papsdroidfr/piClock/_docs/20200311_220712.jpg

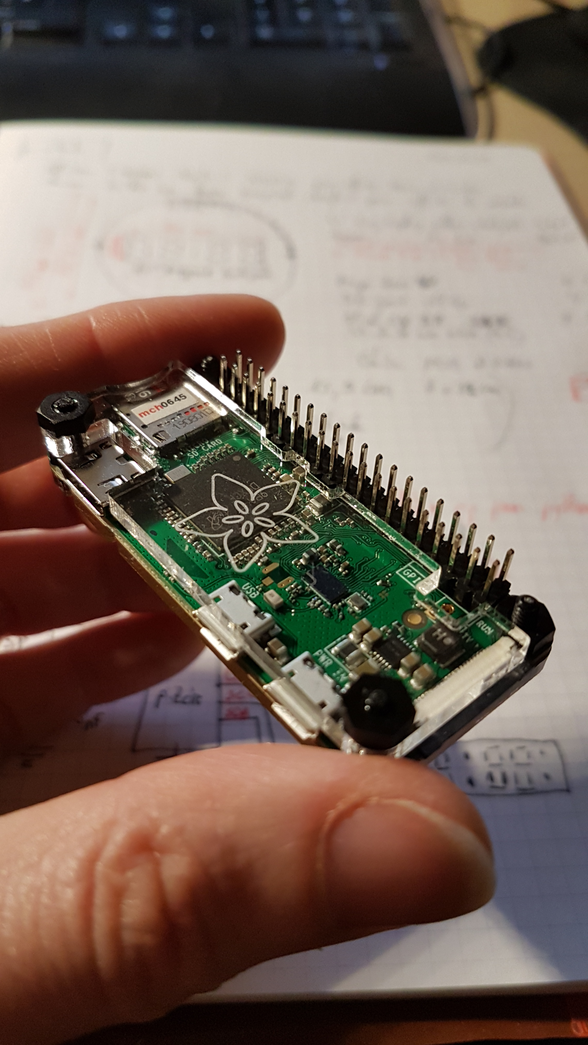
_docs/20200311_220712.jpg
