papsdroidfr/piClock/_docs/20200422_221658.jpg

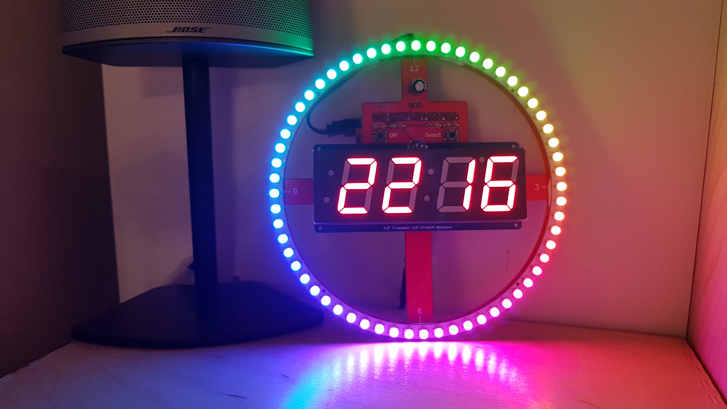
_docs/20200422_221658.jpg
